JoseMDH/Trabajo_Pract_4/sensores/EsquemaFotoResistor/EsquemaFotoResistor.kicad_pcb

## KiCad design Version_4_All-in-one_Controller/docs/Schematic/Schematic.kicad_sch

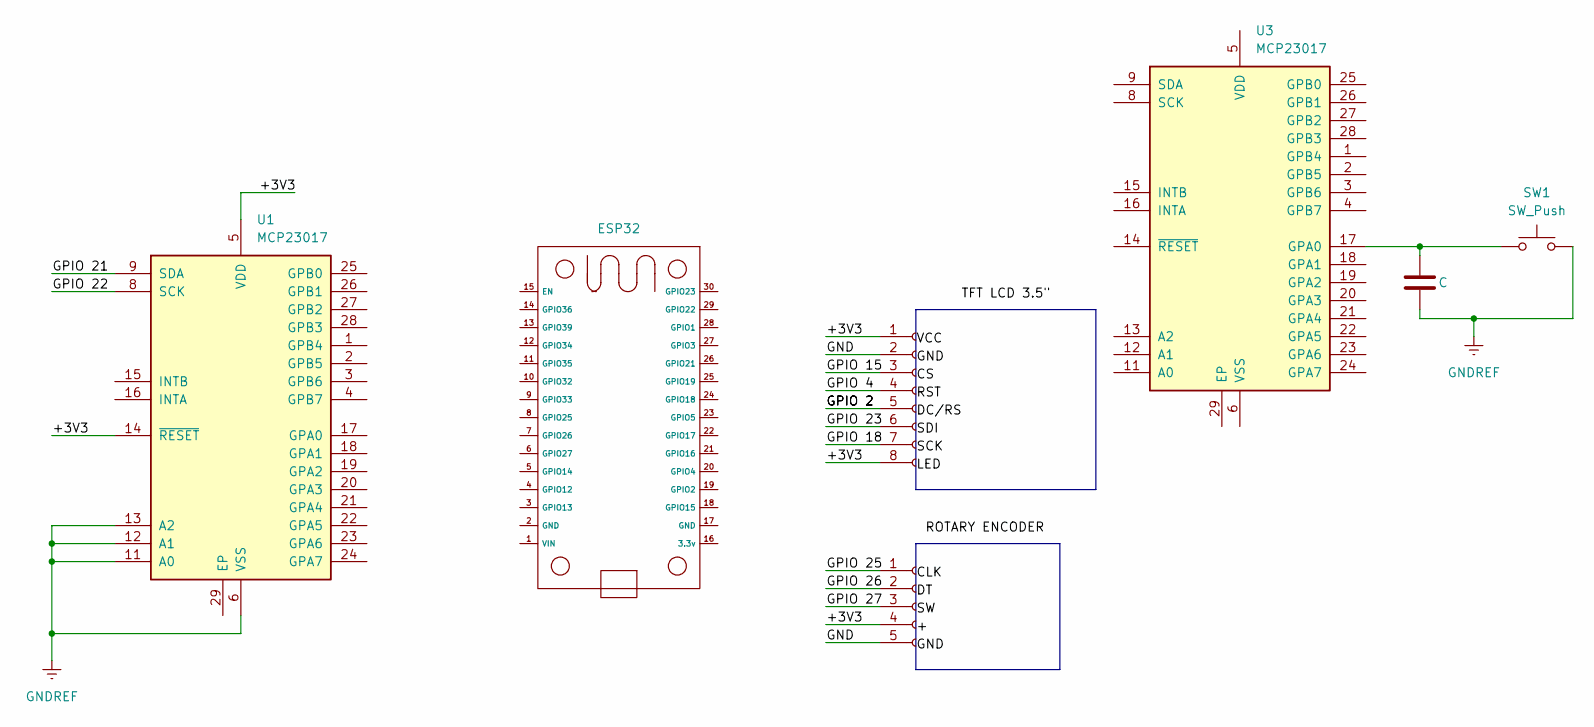
[picture p13: schematic Schematic.kicad_sch]

Parts:
C1: C
J1: Conn_01x08_Socket
J2: Conn_01x05_Socket
SW1: SW_Push
U1, U3: MCP23017; QFN-28-1EP_6x6mm_P0.65mm_EP4.25x4.25mm
U2: ESP32

Connections:
+3V3: J1.1, J1.8, J2.4, U1.5 (VDD), U1.14 (~RESET)
GND: J1.2, J2.5
GNDREF: C1.2, SW1.2, U1.6 (VSS), U1.11 (A0), U1.12 (A1), U1.13 (A2)
GPIO 2: J1.5
GPIO 4: J1.4
GPIO 15: J1.3
GPIO 18: J1.7
GPIO 21: U1.9 (SDA)
GPIO 22: U1.8 (SCK)
GPIO 23: J1.6
GPIO 25: J2.1
GPIO 26: J2.2
GPIO 27: J2.3
unnamed: C1.1, SW1.1, U3.17 (GPA0)
